zzeneg/stront/case/mx38/top.png

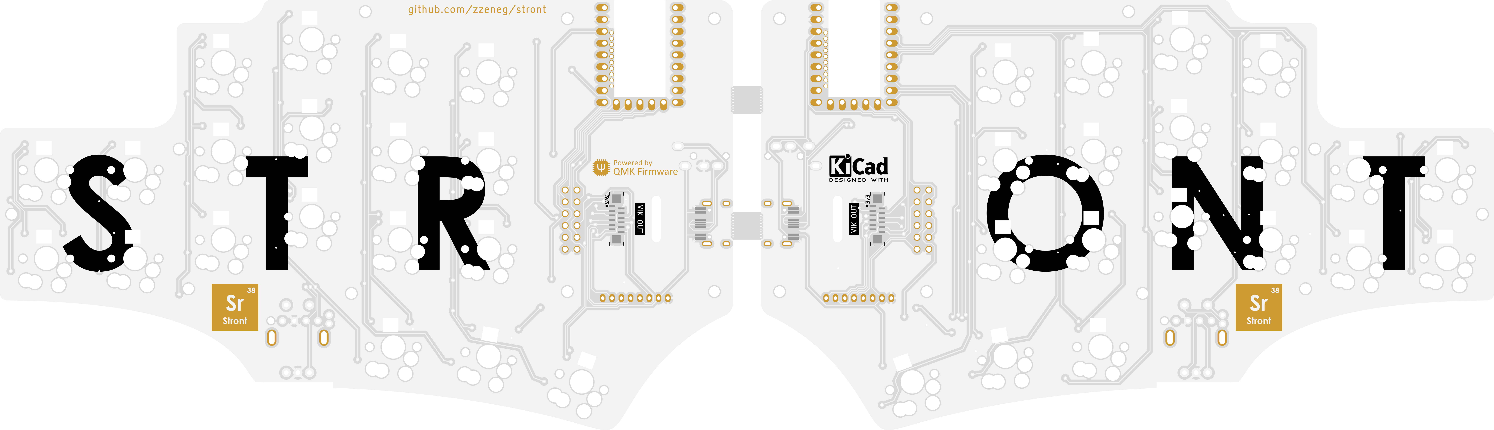
case/mx38/top.png
