zzeneg/stront/images/mx2.jpg

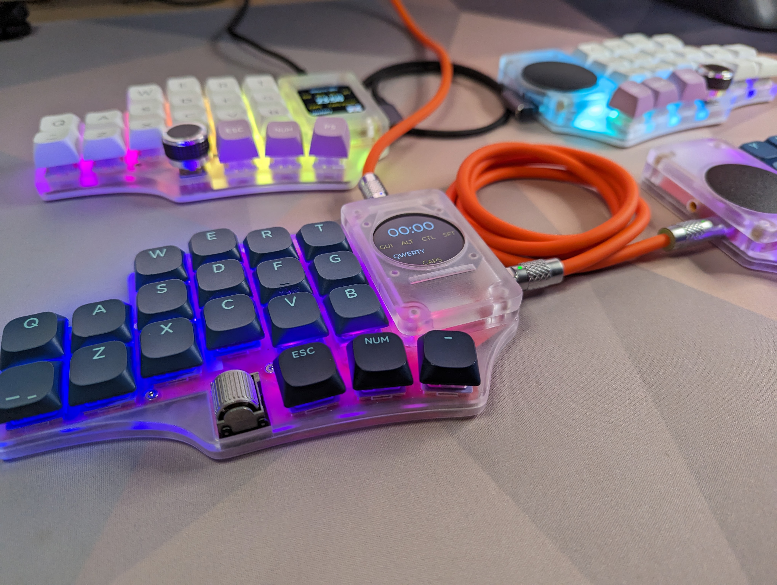
images/mx2.jpg
