zzeneg/stront/images/mx3.jpg

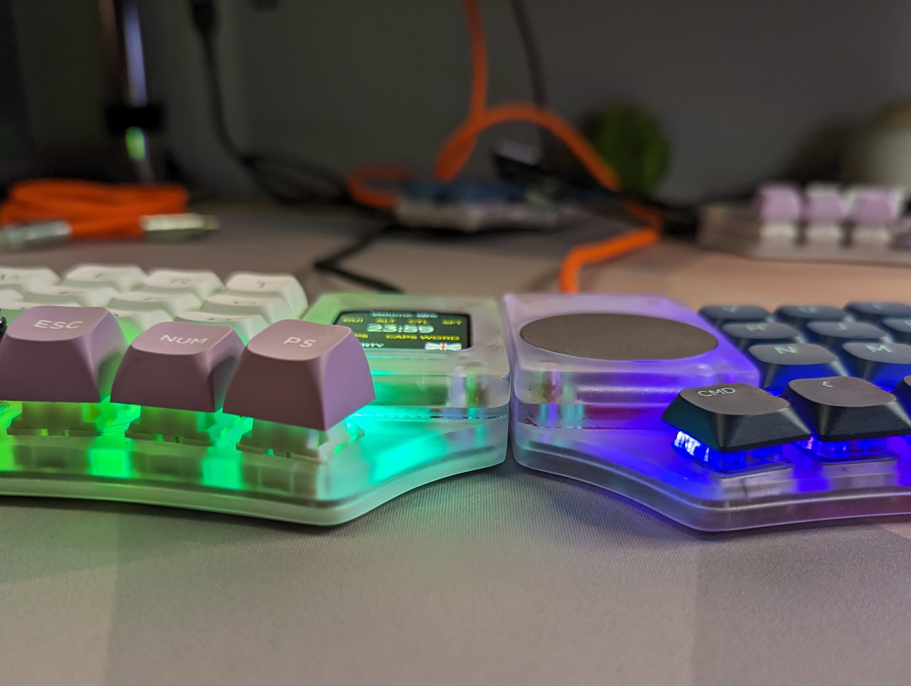
images/mx3.jpg
