zzeneg/stront/images/mx-bottom.jpg

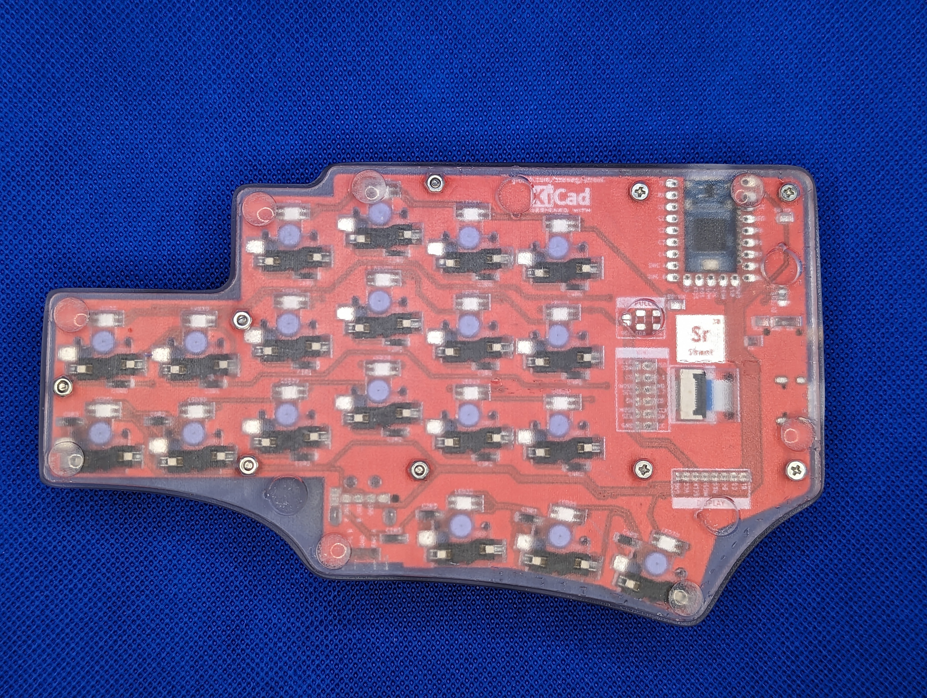
images/mx-bottom.jpg
