zzeneg/stront/images/mx-des.jpg

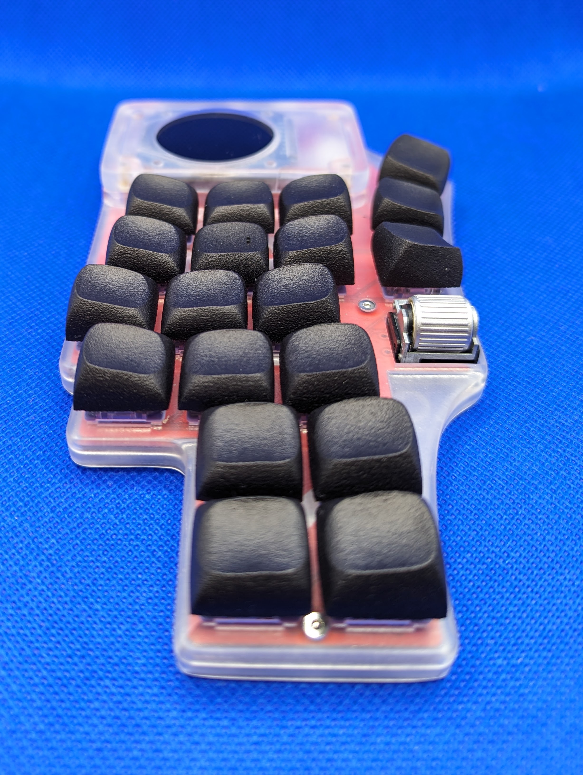
images/mx-des.jpg
