zzeneg/stront/images/mx-pcb.jpg

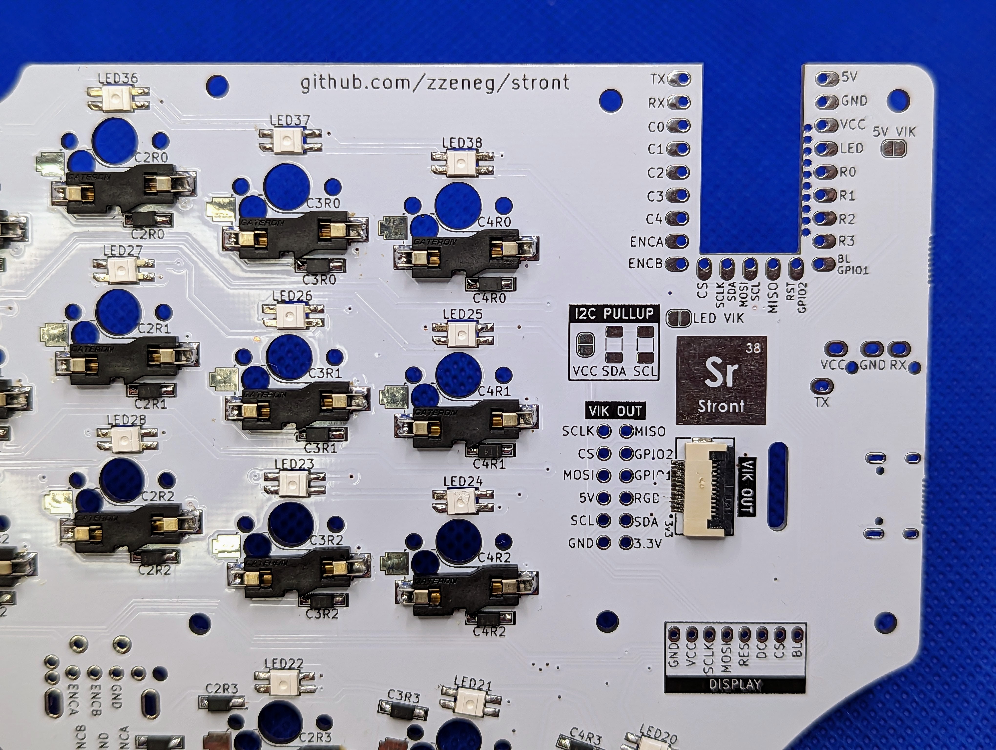
images/mx-pcb.jpg
