zzeneg/stront/images/pcb.jpg

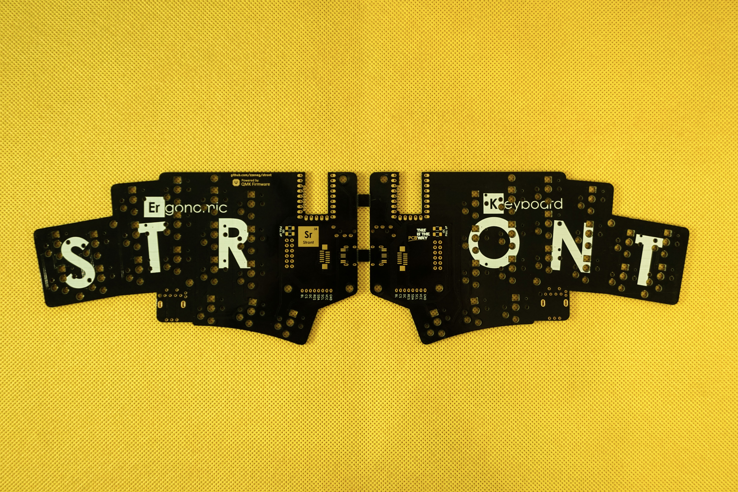
images/pcb.jpg
