zzeneg/stront/images/renders/bottom-inside.png

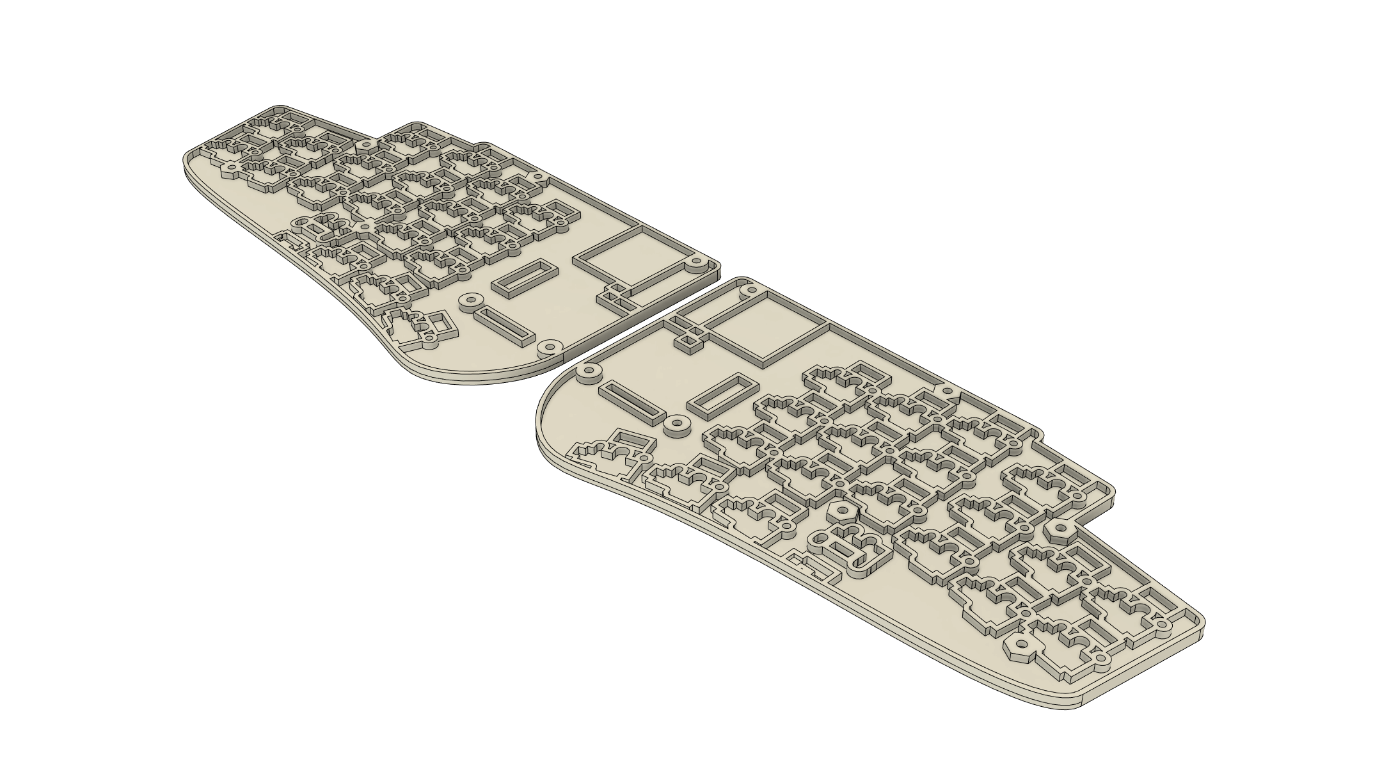
images/renders/bottom-inside.png
