zzeneg/stront/images/renders/bottom-thin.png

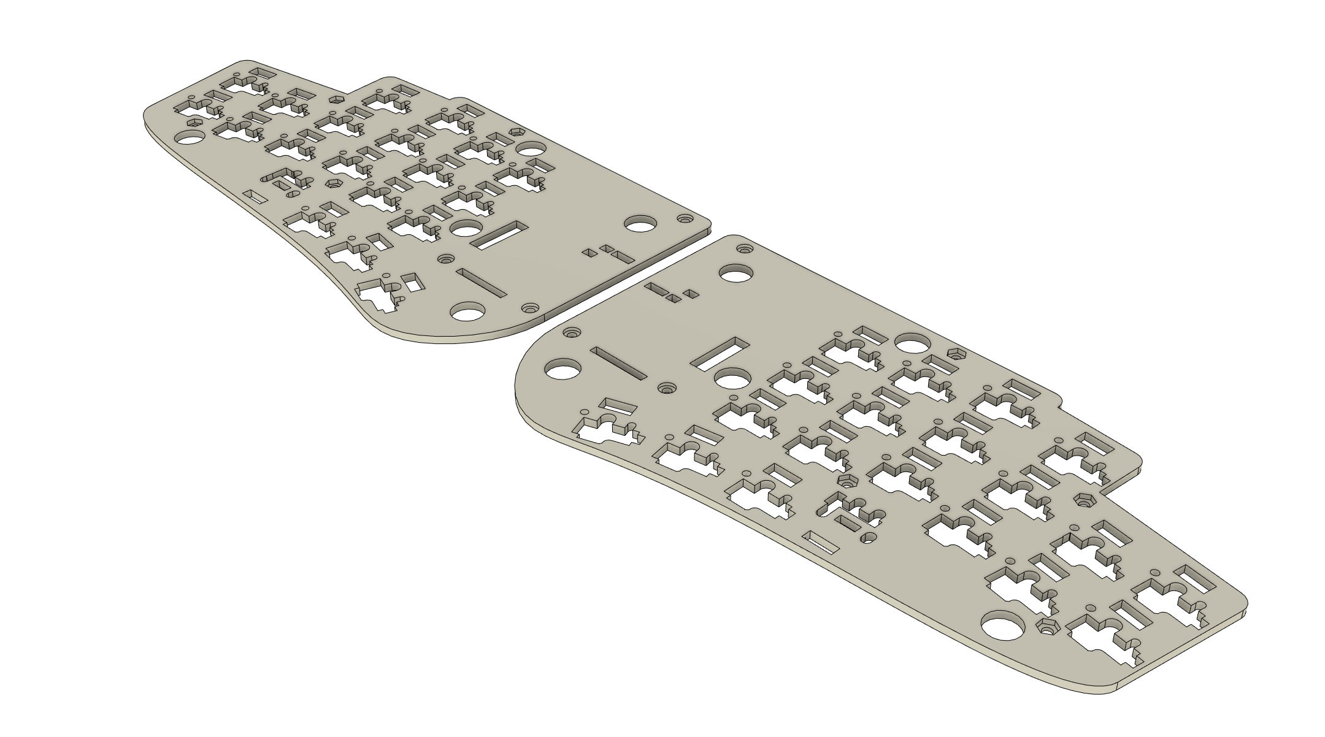
images/renders/bottom-thin.png
