zzeneg/stront/images/renders/case-underside.png

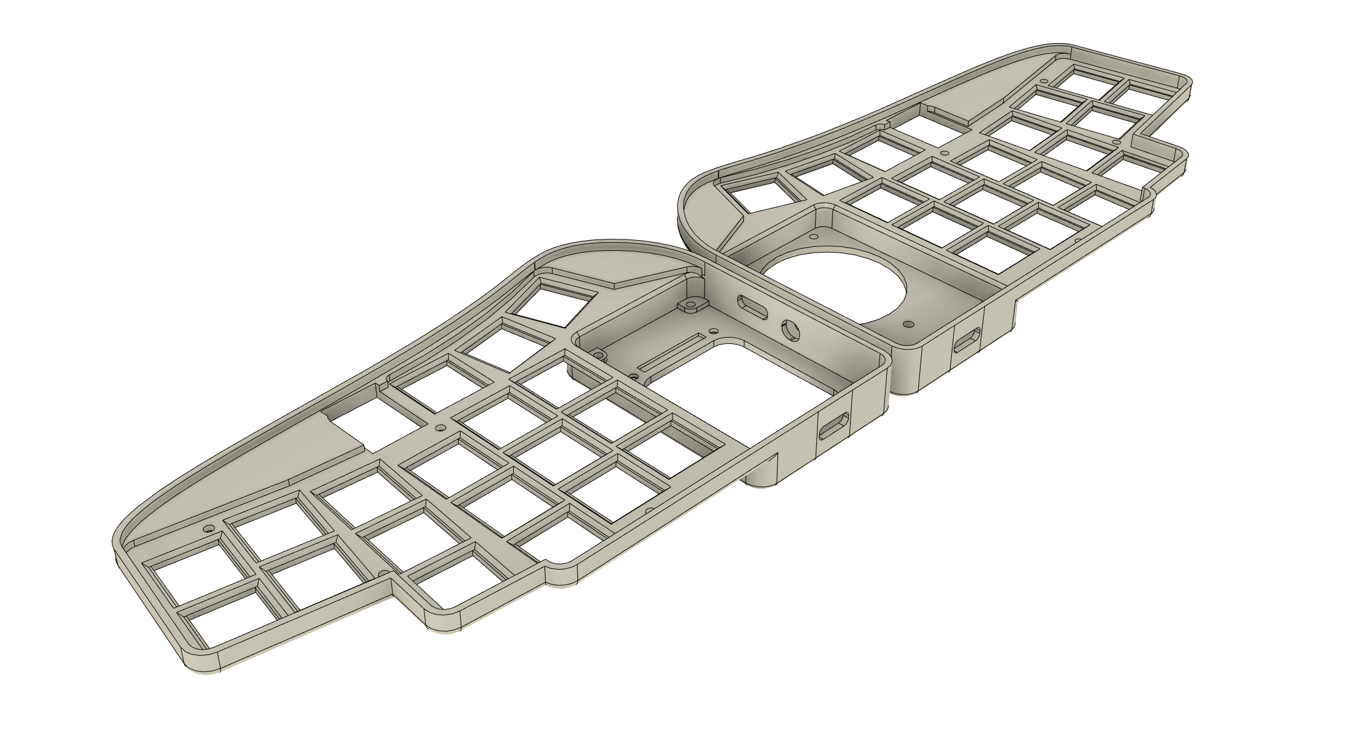
images/renders/case-underside.png
