zzeneg/stront/images/renders/case.png

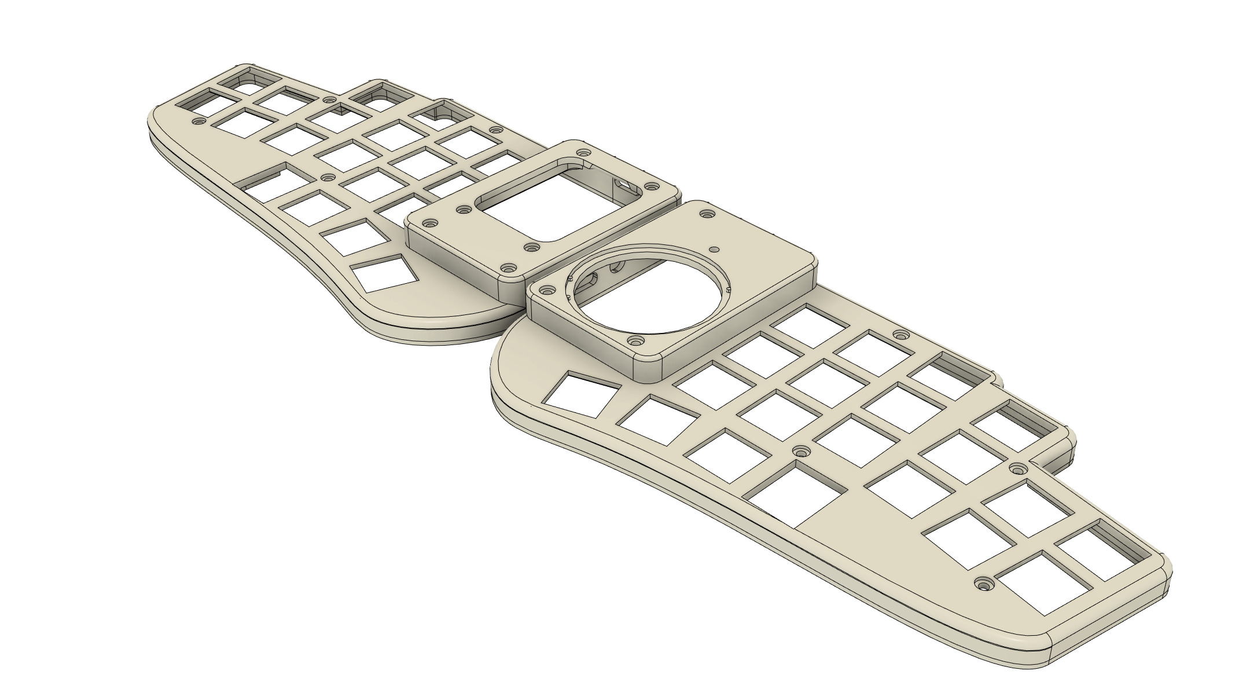
images/renders/case.png
