zzeneg/stront/images/renders/mx40-top.png

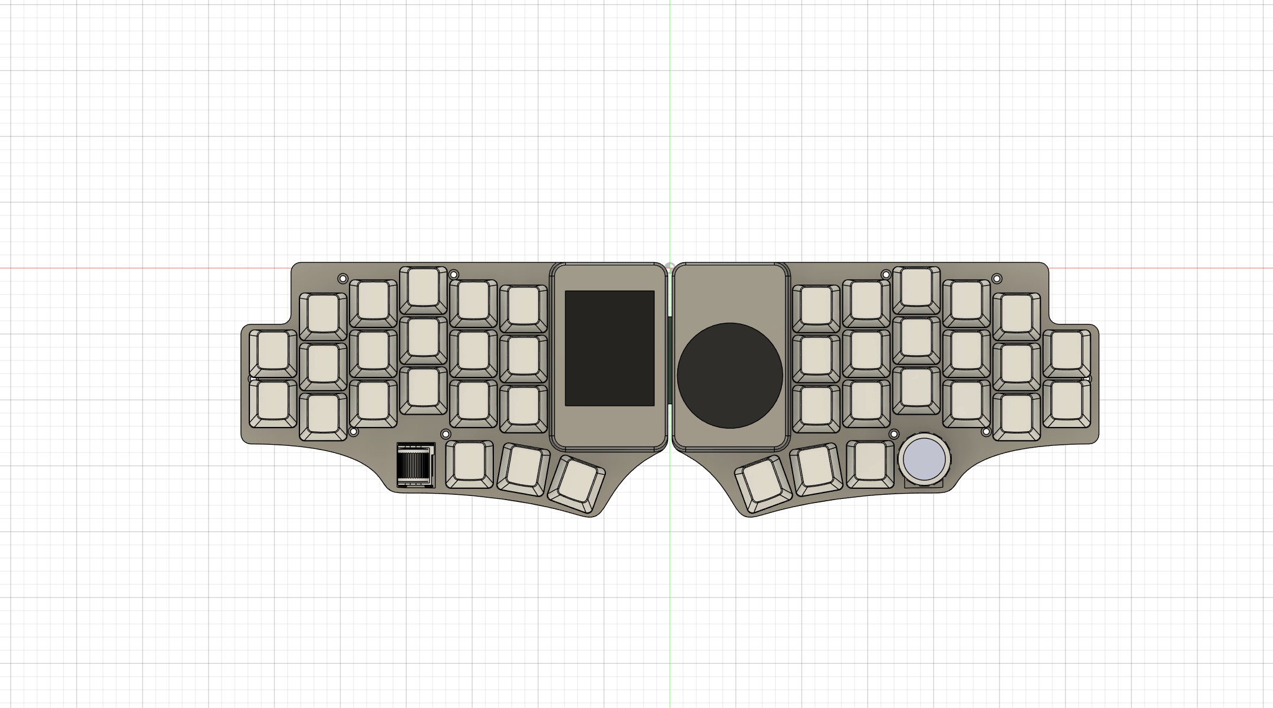
images/renders/mx40-top.png
