zzeneg/stront/images/renders/mx-bottom.png

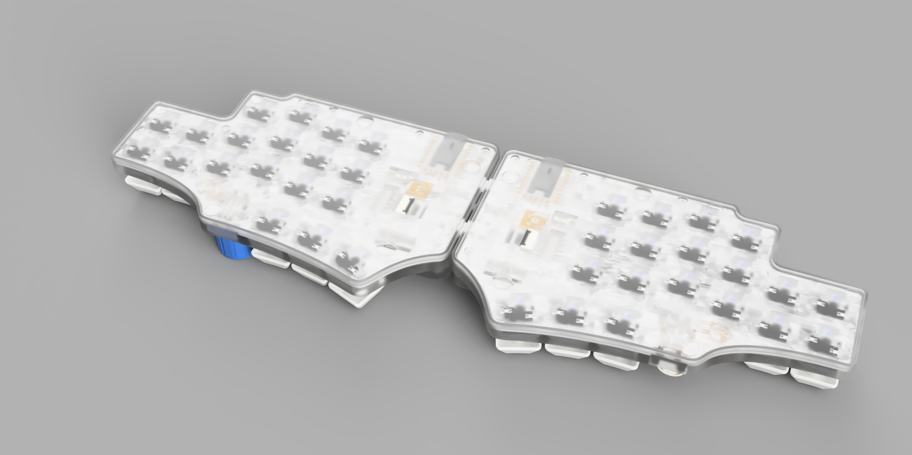
images/renders/mx-bottom.png
