zzeneg/stront/images/renders/mx-pcb.png

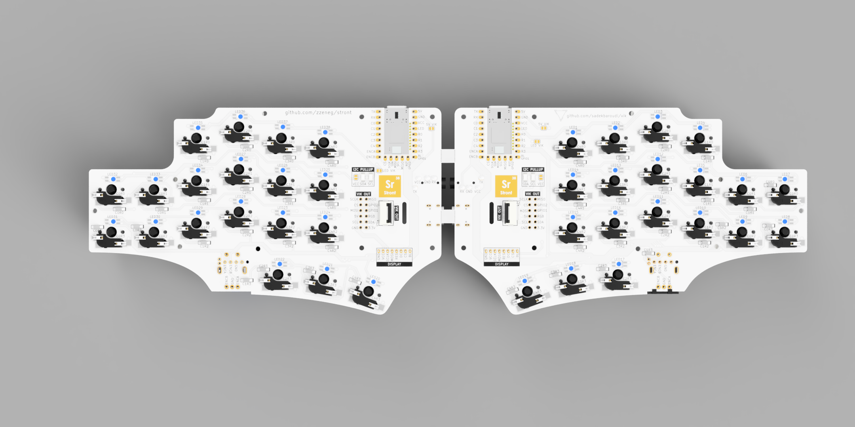
images/renders/mx-pcb.png
