zzeneg/stront/images/renders/mx-top.png

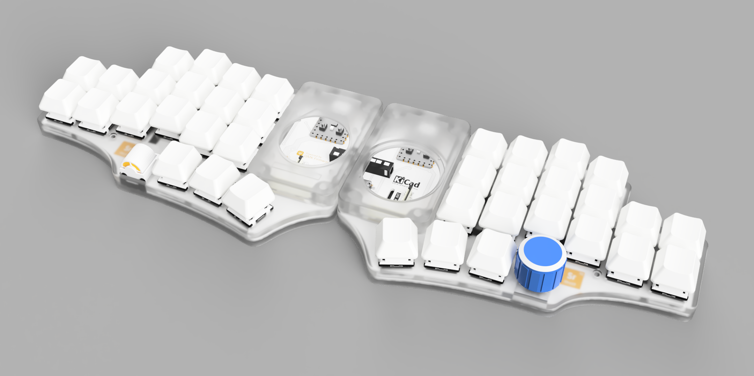
images/renders/mx-top.png
