zzeneg/stront/images/renders/pcb-back.png

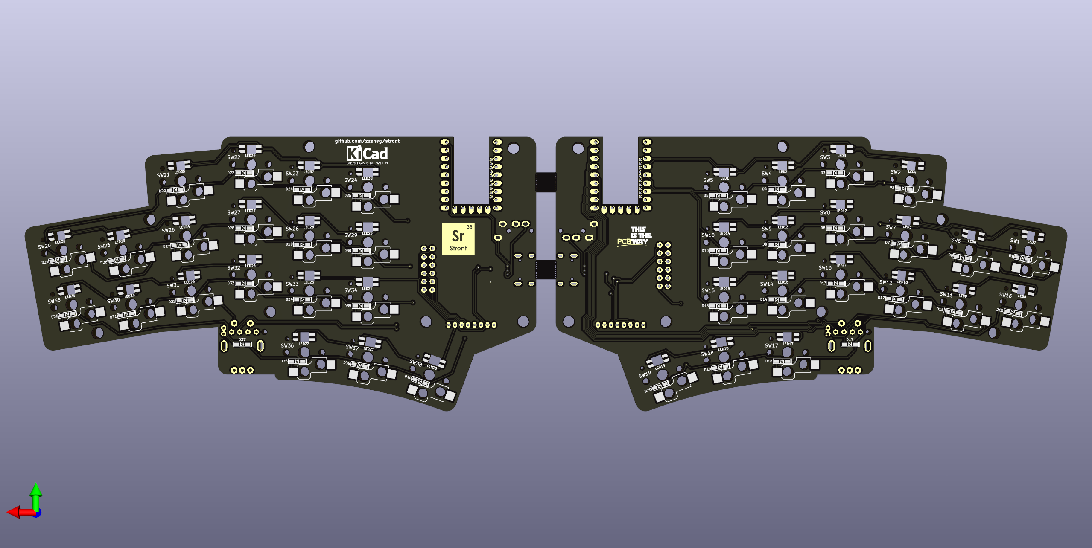
images/renders/pcb-back.png
