zzeneg/stront/images/sunset.jpg

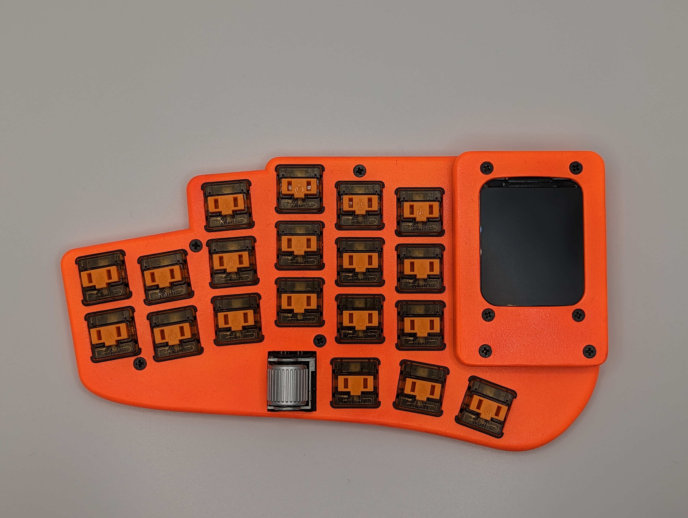
images/sunset.jpg
