zzeneg/stront/images/tps43.jpg

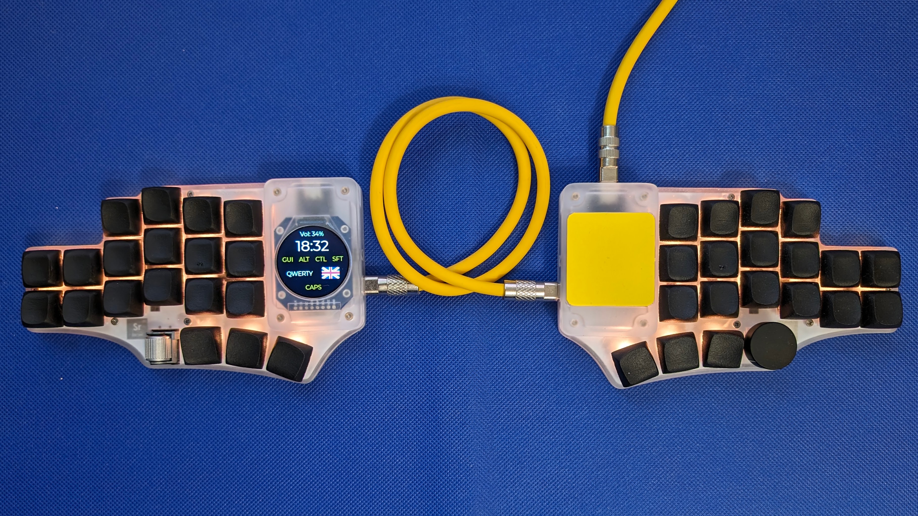
images/tps43.jpg
