zzeneg/stront/images/tps65.jpg

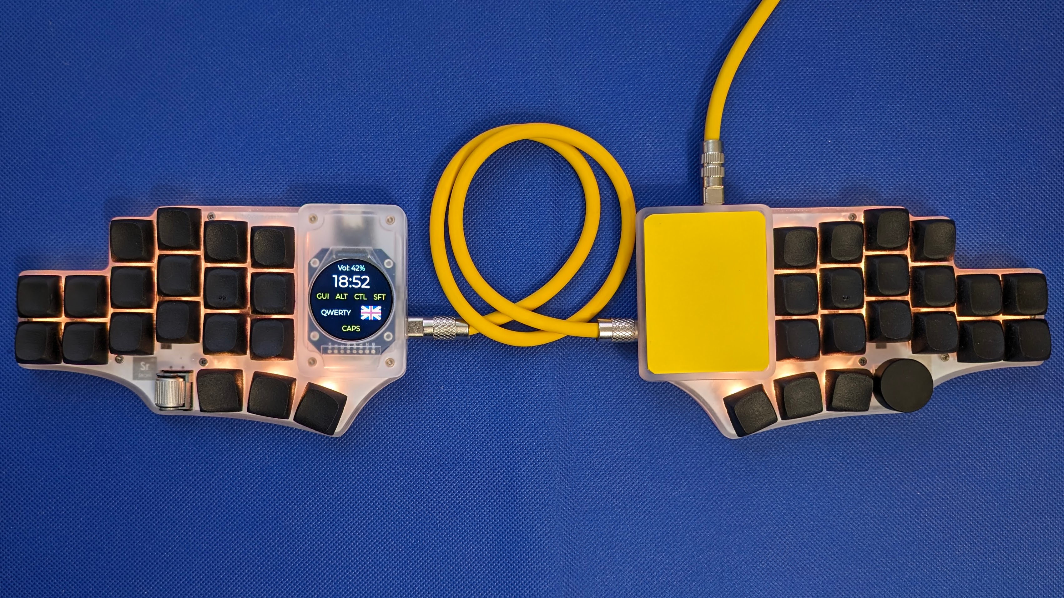
images/tps65.jpg
