zzeneg/stront/case/covers/display-round.stl

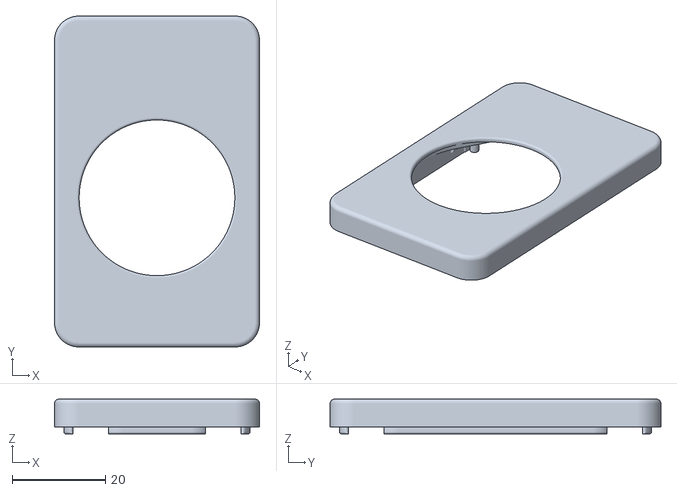
[picture p37: CAD file, 2024-05-09]
case/covers/display-round.stl
44.0 x 71.0 x 7.50
