zzeneg/stront/case/choc/top_case-choc v13_left-thin.stl

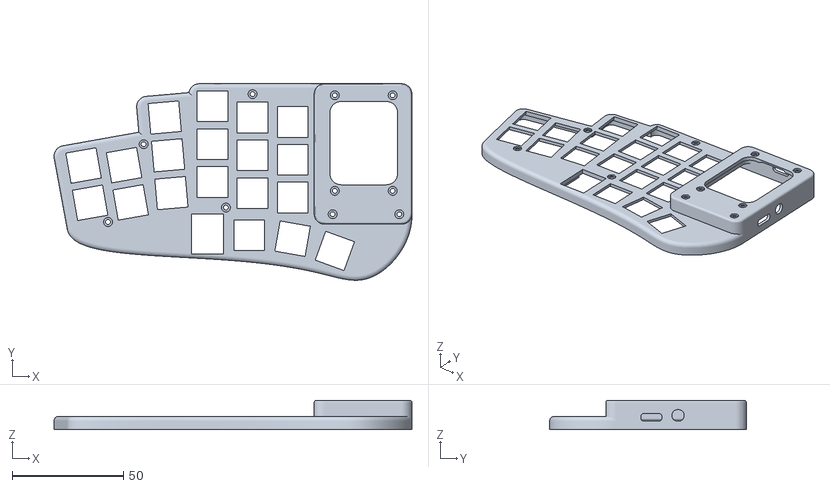
[picture p38: CAD file, 2023-04-07]
case/choc/top_case-choc v13_left-thin.stl
161.0 x 88.4 x 13.2
