zzeneg/stront/case/mx38/bottom_left-shell.stl

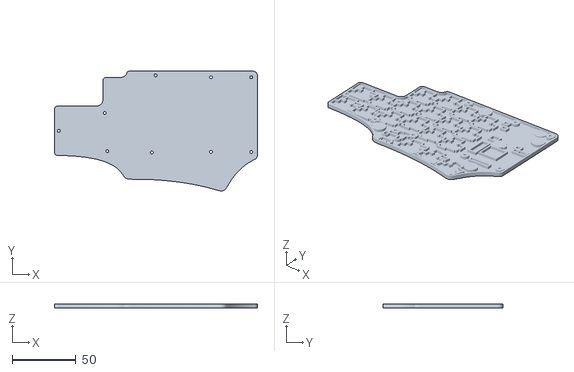
[picture p39: CAD file, 2023-07-26]
case/mx38/bottom_left-shell.stl
159.3 x 94.1 x 3.20
