zzeneg/stront/case/covers/azoteq-tps43.stl

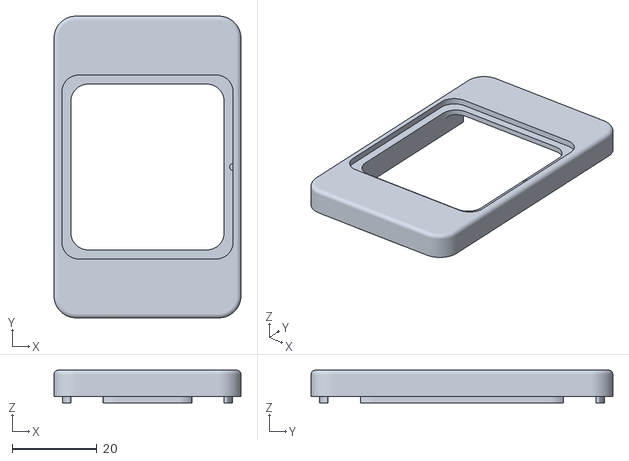
[picture p40: CAD file, 2024-05-09]
case/covers/azoteq-tps43.stl
44.0 x 71.0 x 7.70
