zzeneg/stront/case/covers/display-2inch.stl

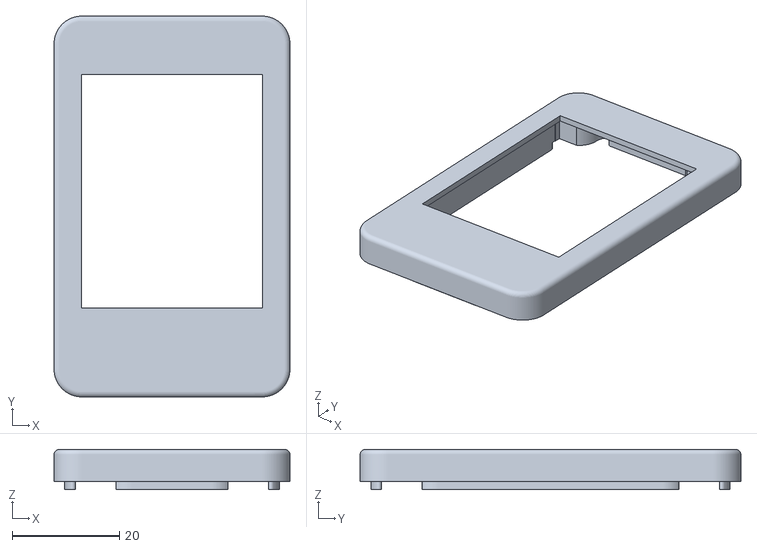
[picture p41: CAD file, 2024-05-09]
case/covers/display-2inch.stl
44.0 x 71.0 x 7.50
