zzeneg/stront/case/mx38/bottom_right.stl

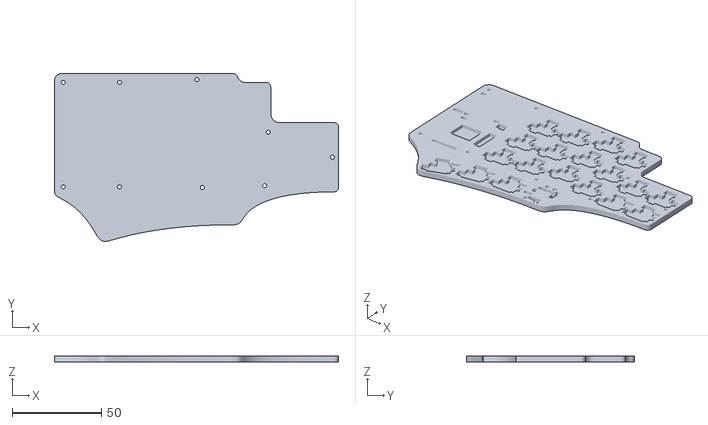
[picture p42: CAD file, 2023-07-26]
case/mx38/bottom_right.stl
159.3 x 94.1 x 3.20
