zzeneg/stront/case/choc/border.dxf

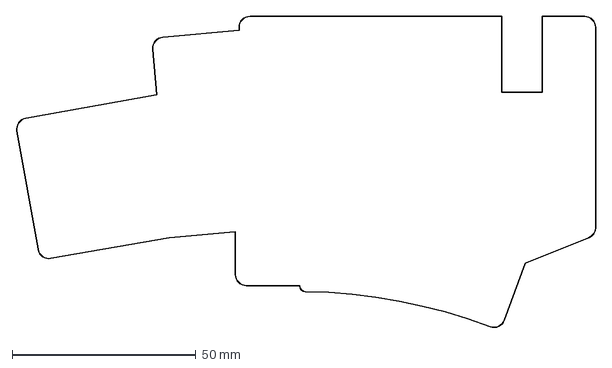
[picture p43: CAD file, 2023-03-06]
case/choc/border.dxf
157.6 x 84.7 mm
