zzeneg/stront/case/mx38/outline.dxf

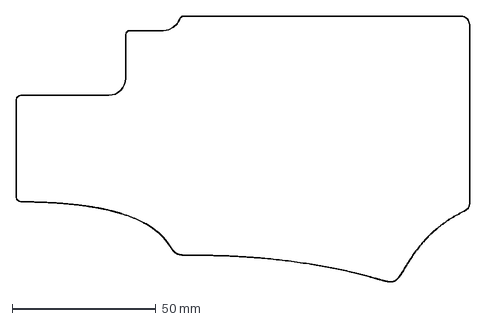
[picture p44: CAD file, 2023-07-26]
case/mx38/outline.dxf
157.5 x 92.3 mm
