zzeneg/stront/build-guide/mx/06.jpg

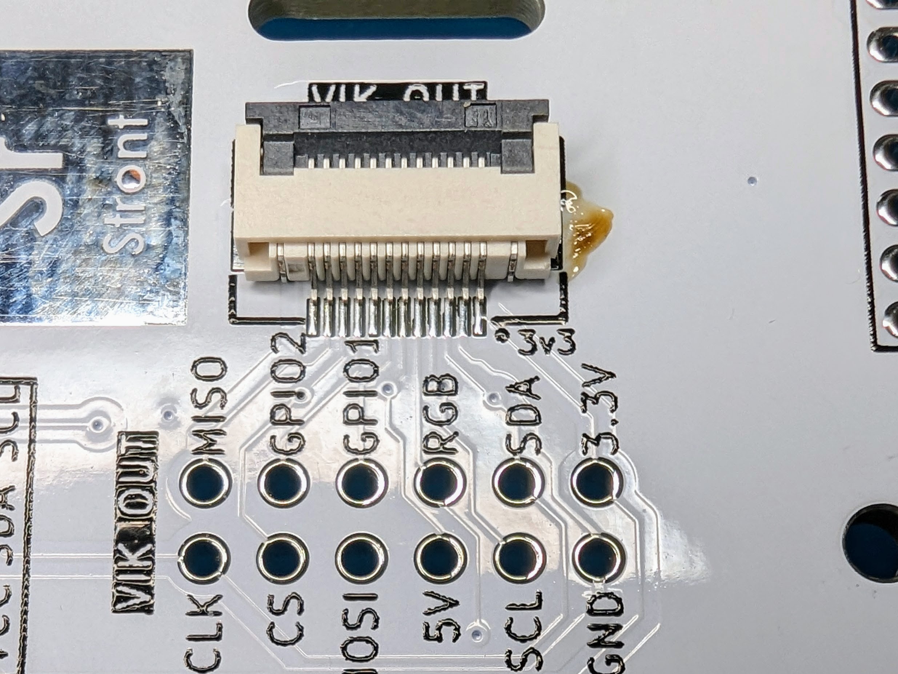
build-guide/mx/06.jpg
