zzeneg/stront/build-guide/mx/07.jpg

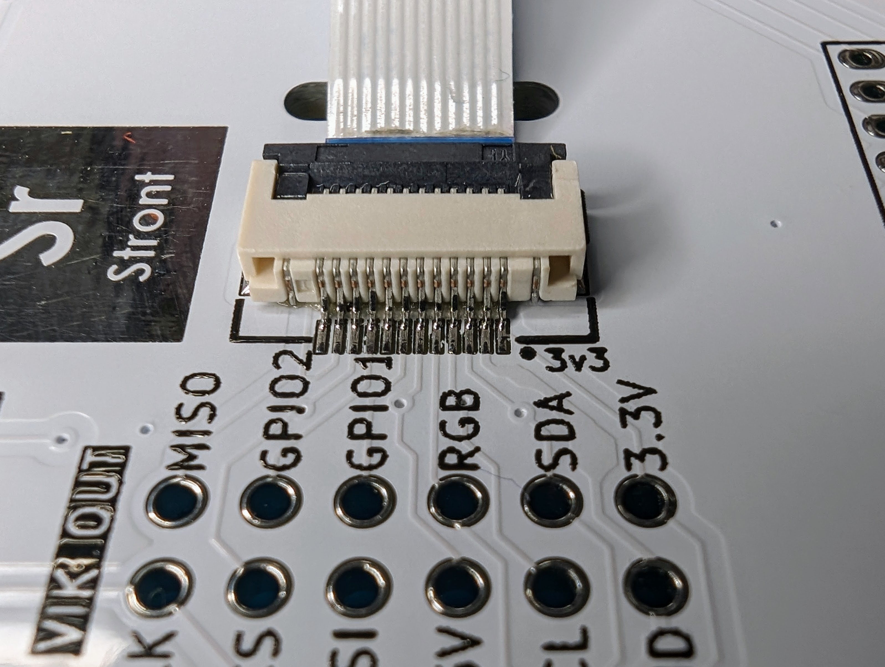
build-guide/mx/07.jpg
